okiraku-camera/nkc70_keyboard/pcb/nkc70_22.kicad_sch

## KiCad design pcb/nkc70_22.kicad_sch (2026-06-21)

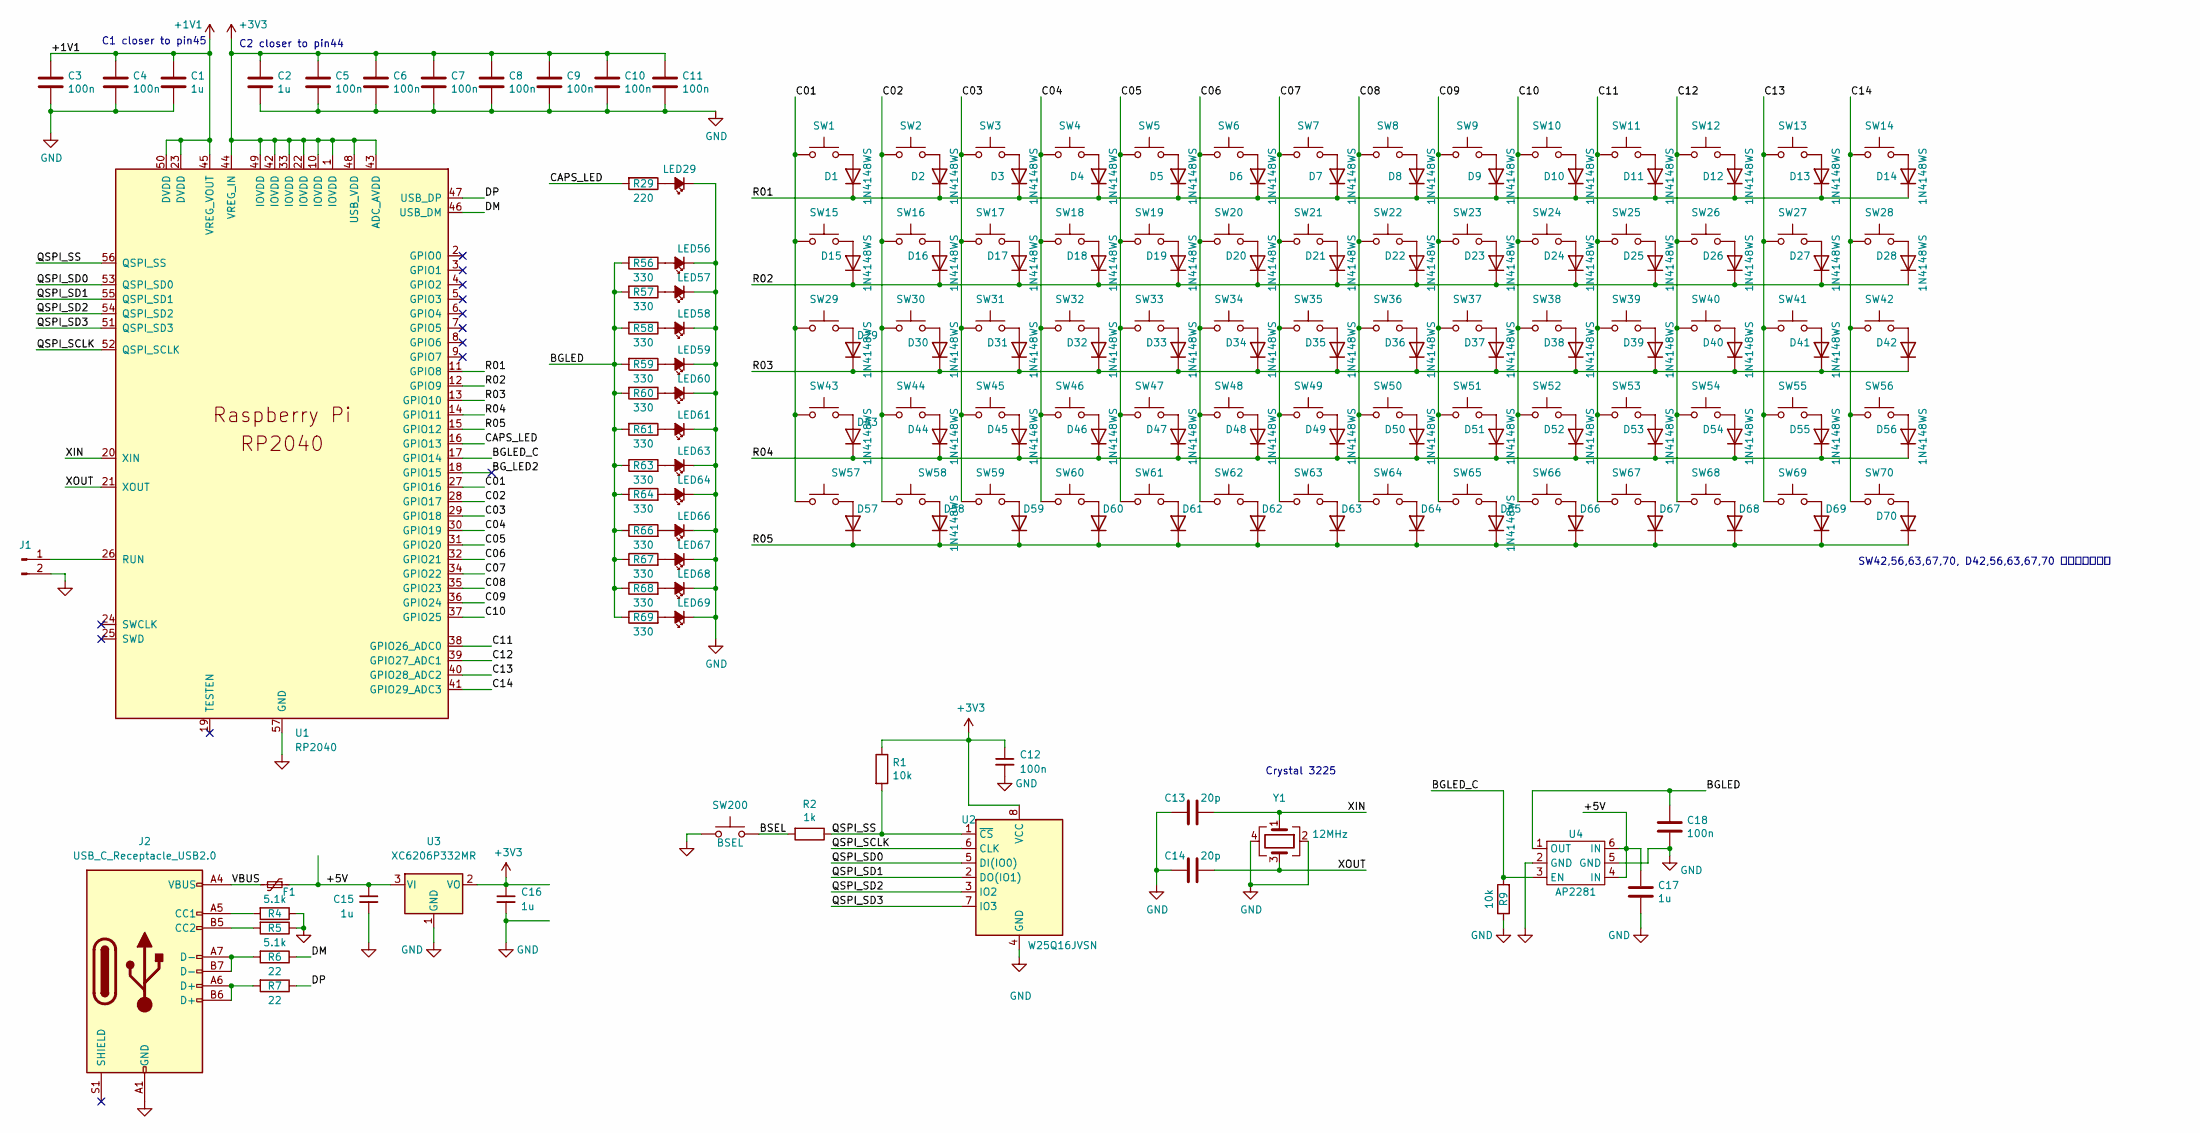
[picture p7: schematic nkc70_22.kicad_sch]

Parts:
C1, C2, C15, C16, C17: 1u; C_0402_1005Metric
C3, C4, C5, C6, C7, C8, C9, C10, C11, C12, C18: 100n; C_0402_1005Metric
C13, C14: 20p; C_0402_1005Metric
D1, D2, D3, D4, D5, D6, D7, D8, D9, D10, D11, D12, D13, D14, D15, D16, D17, D18, D19, D20, D21, D22, D23, D24, D25, D26, D27, D28, D29, D30, D31, D32, D33, D34, D35, D36, D37, D38, D39, D40, D41, D42, D43, D44, D45, D46, D47, D48, D49, D50, D51, D52, D53, D54, D55, D56, D57, D58, D59, D60, D61, D62, D63, D64, D65, D66, D67, D68, D69, D70: 1N4148WS; D_SOD-323
F1: Polyfuse_Small; Fuse_1206_3216Metric
J1: Conn_01x02_Pin; PinHeader_2x01_P2.54mm_Vertical
J2: USB_C_Receptacle_USB2.0; USB_C_Receptacle_304J-BCP16
LED29, LED56, LED57, LED58, LED59, LED60, LED61, LED63, LED64, LED66, LED67, LED68, LED69: LED; LED_1206_3216Metric_Pad1.42x1.75mm_HandSolder
R1, R9: 10k; R_0402_1005Metric
R2: 1k; R_0402_1005Metric
R4, R5: 5.1k; R_0402_1005Metric
R6, R7: 22; R_0402_1005Metric
R29: 220; R_0402_1005Metric
R56, R57, R58, R59, R60, R61, R63, R64, R66, R67, R68, R69: 330; R_0402_1005Metric
SW1, SW2, SW3, SW4, SW5, SW6, SW7, SW8, SW9, SW10, SW11, SW12, SW13, SW14, SW15, SW16, SW17, SW18, SW19, SW20, SW21, SW22, SW23, SW24, SW25, SW26, SW27, SW28, SW29, SW30, SW31, SW32, SW33, SW34, SW35, SW36, SW37, SW38, SW39, SW40, SW41, SW44, SW45, SW46, SW47, SW48, SW49, SW50, SW51, SW52, SW53, SW54, SW55, SW57, SW58, SW59, SW60, SW61, SW62, SW63, SW64, SW65, SW66, SW68, SW69: SW_Push
SW42: SW_Push; SW_Kailh_Choc_V1_1.50u
SW43: SW_Push; ChocV1_2.00u_stabilizer_PCB
SW56, SW67, SW70: SW_Push; SW_Kailh_Choc_V1_1.00u
SW200: BSEL; SW_SPST_TL3342
U1: RP2040; RP2040-QFN-56
U2: W25Q16JVSN; SOP-8_3.9x4.9mm_P1.27mm
U3: XC6206P332MR; SOT-23-3
U4: AP2281; SOT-23-6
Y1: 12MHz; Crystal_SMD_3225-4Pin_3.2x2.5mm

Connections:
+1V1: C1.1, C3.1, C4.1, U1.23 (DVDD), U1.45 (VREG_VOUT), U1.50 (DVDD)
+3V3: C2.1, C5.1, C6.1, C7.1, C8.1, C9.1, C10.1, C11.1, C12.1, C16.1, R1.1, U1.1 (IOVDD), U1.10 (IOVDD), U1.22 (IOVDD), U1.33 (IOVDD), U1.42 (IOVDD), U1.43 (ADC_AVDD), U1.44 (VREG_IN), U1.48 (USB_VDD), U1.49 (IOVDD), U2.8 (VCC), U3.2 (VO)
+5V: C15.1, C17.1, F1.1, U3.3 (VI), U4.4 (IN), U4.6 (IN)
BGLED: C18.1, R56.2, R57.2, R58.2, R59.2, R60.2, R61.2, R63.1, R64.1, R66.1, R67.1, R68.1, R69.1, U4.1 (OUT)
BGLED_C: R9.2, U1.17 (GPIO14), U4.3 (EN)
BG_LED2: U1.18 (GPIO15)
BSEL: R2.2, SW200.2
C01: SW1.1, SW15.1, SW29.1, SW43.1, SW57.1, U1.27 (GPIO16)
C02: SW2.1, SW16.1, SW30.1, SW44.1, SW58.1, U1.28 (GPIO17)
C03: SW3.1, SW17.1, SW31.1, SW45.1, SW59.1, U1.29 (GPIO18)
C04: SW4.1, SW18.1, SW32.1, SW46.1, SW60.1, U1.30 (GPIO19)
C05: SW5.1, SW19.1, SW33.1, SW47.1, SW61.1, U1.31 (GPIO20)
C06: SW6.1, SW20.1, SW34.1, SW48.1, SW62.1, U1.32 (GPIO21)
C07: SW7.1, SW21.1, SW35.1, SW49.1, SW63.1, U1.34 (GPIO22)
C08: SW8.1, SW22.1, SW36.1, SW50.1, SW64.1, U1.35 (GPIO23)
C09: SW9.1, SW23.1, SW37.1, SW51.1, SW65.1, U1.36 (GPIO24)
C10: SW10.1, SW24.1, SW38.1, SW52.1, SW66.1, U1.37 (GPIO25)
C11: SW11.1, SW25.1, SW39.1, SW53.1, SW67.1, U1.38 (GPIO26_ADC0)
C12: SW12.1, SW26.1, SW40.1, SW54.1, SW68.1, U1.39 (GPIO27_ADC1)
C13: SW13.1, SW27.1, SW41.1, SW55.1, SW69.1, U1.40 (GPIO28_ADC2)
C14: SW14.1, SW28.1, SW42.1, SW56.1, SW70.1, U1.41 (GPIO29_ADC3)
CAPS_LED: R29.2, U1.16 (GPIO13)
DM: R6.1, U1.46 (USB_DM)
DP: R7.1, U1.47 (USB_DP)
GND: C1.2, C2.2, C3.2, C4.2, C5.2, C6.2, C7.2, C8.2, C9.2, C10.2, C11.2, C12.2, C13.2, C14.2, C15.2, C16.2, C17.2, C18.2, J1.2, J2.A1 (GND), J2.A12 (GND), J2.B1 (GND), J2.B12 (GND), LED29.1 (K), LED56.1 (K), LED57.1 (K), LED58.1 (K), LED59.1 (K), LED60.1 (K), LED61.1 (K), LED63.1 (K), LED64.1 (K), LED66.1 (K), LED67.1 (K), LED68.1 (K), LED69.1 (K), R4.1, R5.1, R9.1, SW200.1, U1.57 (GND), U2.4 (GND), U3.1 (GND), U4.2 (GND), U4.5 (GND), Y1.2, Y1.4
unnamed: D1.2 (A), SW1.2
unnamed: D2.2 (A), SW2.2
unnamed: D3.2 (A), SW3.2
unnamed: D4.2 (A), SW4.2
unnamed: D5.2 (A), SW5.2
unnamed: D6.2 (A), SW6.2
unnamed: D7.2 (A), SW7.2
unnamed: D8.2 (A), SW8.2
unnamed: D9.2 (A), SW9.2
unnamed: D10.2 (A), SW10.2
unnamed: D11.2 (A), SW11.2
unnamed: D12.2 (A), SW12.2
unnamed: D13.2 (A), SW13.2
unnamed: D14.2 (A), SW14.2
unnamed: D15.2 (A), SW15.2
unnamed: D16.2 (A), SW16.2
unnamed: D17.2 (A), SW17.2
unnamed: D18.2 (A), SW18.2
unnamed: D19.2 (A), SW19.2
unnamed: D20.2 (A), SW20.2
unnamed: D21.2 (A), SW21.2
unnamed: D22.2 (A), SW22.2
unnamed: D23.2 (A), SW23.2
unnamed: D24.2 (A), SW24.2
unnamed: D25.2 (A), SW25.2
unnamed: D26.2 (A), SW26.2
unnamed: D27.2 (A), SW27.2
unnamed: D28.2 (A), SW28.2
unnamed: D29.2 (A), SW29.2
unnamed: D30.2 (A), SW30.2
unnamed: D31.2 (A), SW31.2
unnamed: D32.2 (A), SW32.2
unnamed: D33.2 (A), SW33.2
unnamed: D34.2 (A), SW34.2
unnamed: D35.2 (A), SW35.2
unnamed: D36.2 (A), SW36.2
unnamed: D37.2 (A), SW37.2
unnamed: D38.2 (A), SW38.2
unnamed: D39.2 (A), SW39.2
unnamed: D40.2 (A), SW40.2
unnamed: D41.2 (A), SW41.2
unnamed: D42.2 (A), SW42.2
unnamed: D43.2 (A), SW43.2
unnamed: D44.2 (A), SW44.2
unnamed: D45.2 (A), SW45.2
unnamed: D46.2 (A), SW46.2
unnamed: D47.2 (A), SW47.2
unnamed: D48.2 (A), SW48.2
unnamed: D49.2 (A), SW49.2
unnamed: D50.2 (A), SW50.2
unnamed: D51.2 (A), SW51.2
unnamed: D52.2 (A), SW52.2
unnamed: D53.2 (A), SW53.2
unnamed: D54.2 (A), SW54.2
unnamed: D55.2 (A), SW55.2
unnamed: D56.2 (A), SW56.2
unnamed: D57.2 (A), SW57.2
unnamed: D58.2 (A), SW58.2
unnamed: D59.2 (A), SW59.2
unnamed: D60.2 (A), SW60.2
unnamed: D61.2 (A), SW61.2
unnamed: D62.2 (A), SW62.2
unnamed: D63.2 (A), SW63.2
unnamed: D64.2 (A), SW64.2
unnamed: D65.2 (A), SW65.2
unnamed: D66.2 (A), SW66.2
unnamed: D67.2 (A), SW67.2
unnamed: D68.2 (A), SW68.2
unnamed: D69.2 (A), SW69.2
unnamed: D70.2 (A), SW70.2
unnamed: J1.1, U1.26 (RUN)
unnamed: J2.A5 (CC1), R4.2
unnamed: J2.A6 (D+), J2.B6 (D+), R7.2
unnamed: J2.A7 (D-), J2.B7 (D-), R6.2
unnamed: J2.B5 (CC2), R5.2
unnamed: LED29.2 (A), R29.1
unnamed: LED56.2 (A), R56.1
unnamed: LED57.2 (A), R57.1
unnamed: LED58.2 (A), R58.1
unnamed: LED59.2 (A), R59.1
unnamed: LED60.2 (A), R60.1
unnamed: LED61.2 (A), R61.1
unnamed: LED63.2 (A), R63.2
unnamed: LED64.2 (A), R64.2
unnamed: LED66.2 (A), R66.2
unnamed: LED67.2 (A), R67.2
unnamed: LED68.2 (A), R68.2
unnamed: LED69.2 (A), R69.2
QSPI_SCLK: U1.52 (QSPI_SCLK), U2.6 (CLK)
QSPI_SD0: U1.53 (QSPI_SD0), U2.5 (DI(IO0))
QSPI_SD1: U1.55 (QSPI_SD1), U2.2 (DO(IO1))
QSPI_SD2: U1.54 (QSPI_SD2), U2.3 (IO2)
QSPI_SD3: U1.51 (QSPI_SD3), U2.7 (IO3)
QSPI_SS: R1.2, R2.1, U1.56 (QSPI_SS), U2.1 (~CS)
R01: D1.1 (K), D2.1 (K), D3.1 (K), D4.1 (K), D5.1 (K), D6.1 (K), D7.1 (K), D8.1 (K), D9.1 (K), D10.1 (K), D11.1 (K), D12.1 (K), D13.1 (K), D14.1 (K), U1.11 (GPIO8)
R02: D15.1 (K), D16.1 (K), D17.1 (K), D18.1 (K), D19.1 (K), D20.1 (K), D21.1 (K), D22.1 (K), D23.1 (K), D24.1 (K), D25.1 (K), D26.1 (K), D27.1 (K), D28.1 (K), U1.12 (GPIO9)
R03: D29.1 (K), D30.1 (K), D31.1 (K), D32.1 (K), D33.1 (K), D34.1 (K), D35.1 (K), D36.1 (K), D37.1 (K), D38.1 (K), D39.1 (K), D40.1 (K), D41.1 (K), D42.1 (K), U1.13 (GPIO10)
R04: D43.1 (K), D44.1 (K), D45.1 (K), D46.1 (K), D47.1 (K), D48.1 (K), D49.1 (K), D50.1 (K), D51.1 (K), D52.1 (K), D53.1 (K), D54.1 (K), D55.1 (K), D56.1 (K), U1.14 (GPIO11)
R05: D57.1 (K), D58.1 (K), D59.1 (K), D60.1 (K), D61.1 (K), D62.1 (K), D63.1 (K), D64.1 (K), D65.1 (K), D66.1 (K), D67.1 (K), D68.1 (K), D69.1 (K), D70.1 (K), U1.15 (GPIO12)
VBUS: F1.2, J2.A4 (VBUS), J2.A9 (VBUS), J2.B4 (VBUS), J2.B9 (VBUS)
XIN: C13.1, U1.20 (XIN), Y1.1
XOUT: C14.1, U1.21 (XOUT), Y1.3

Notes on the sheet:
C2 closer to pin44
C1 closer to pin45
SW42,56,63,67,70, D42,56,63,67,70 は基板にない。
Crystal 3225
